mrrosoff/Polaroid/enclosure/preview/06_side_profile.png

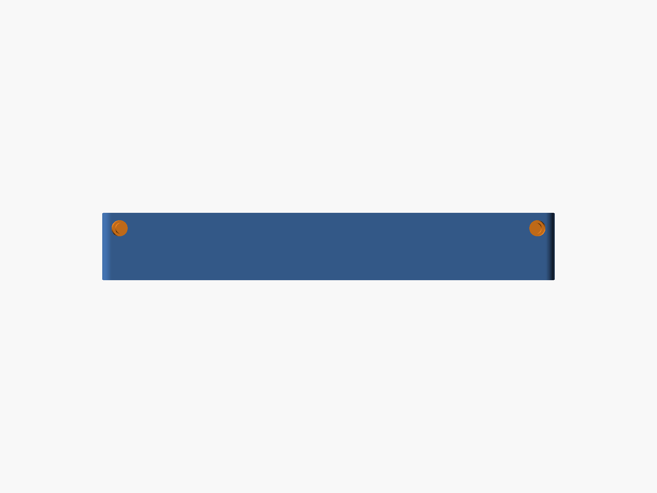
enclosure/preview/06_side_profile.png
