mrrosoff/Polaroid/enclosure/preview/05_assembled.png

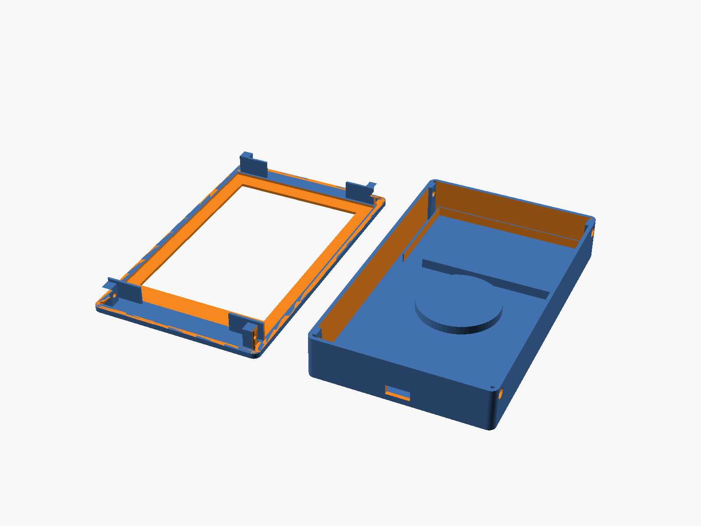
enclosure/preview/05_assembled.png
